ralph-lange/Smart_Home_Boxle/doc/raw_wooden_box.jpg

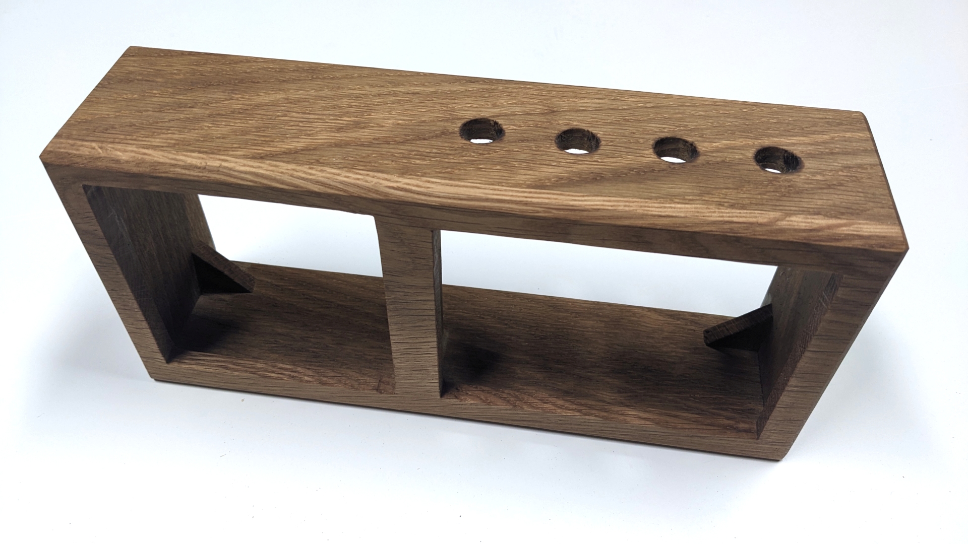
doc/raw_wooden_box.jpg
