ralph-lange/Smart_Home_Boxle/doc/ePaper_SPI_wiring.jpg

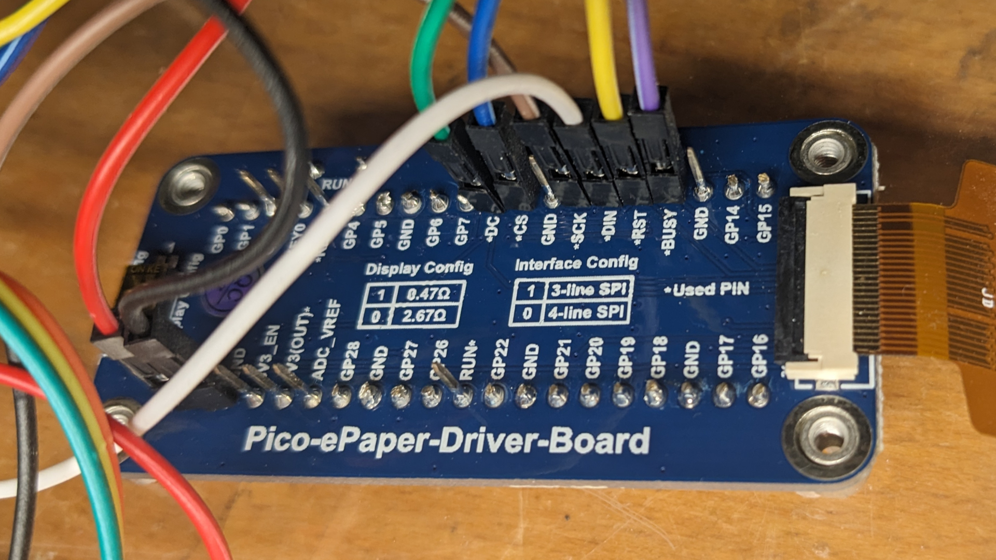
doc/ePaper_SPI_wiring.jpg
